mschaf/hp_dl380_fan_controller/reference images/IMG_20200121_184613.jpg

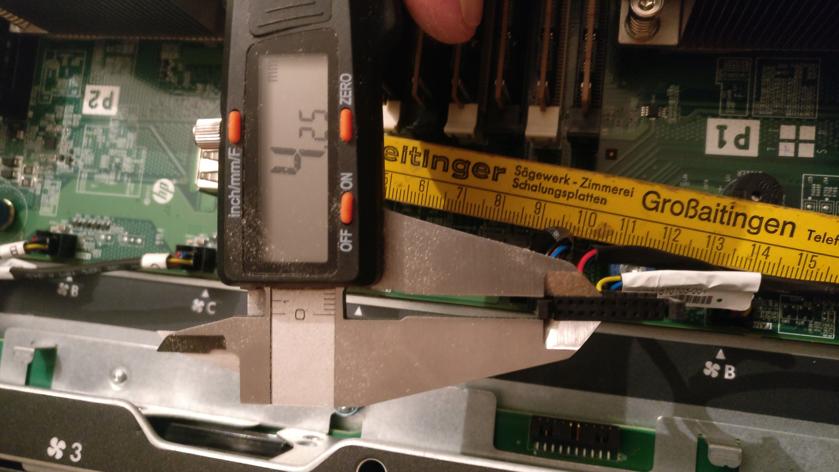
reference images/IMG_20200121_184613.jpg
