mschaf/hp_dl380_fan_controller/reference images/IMG_20200121_184752.jpg

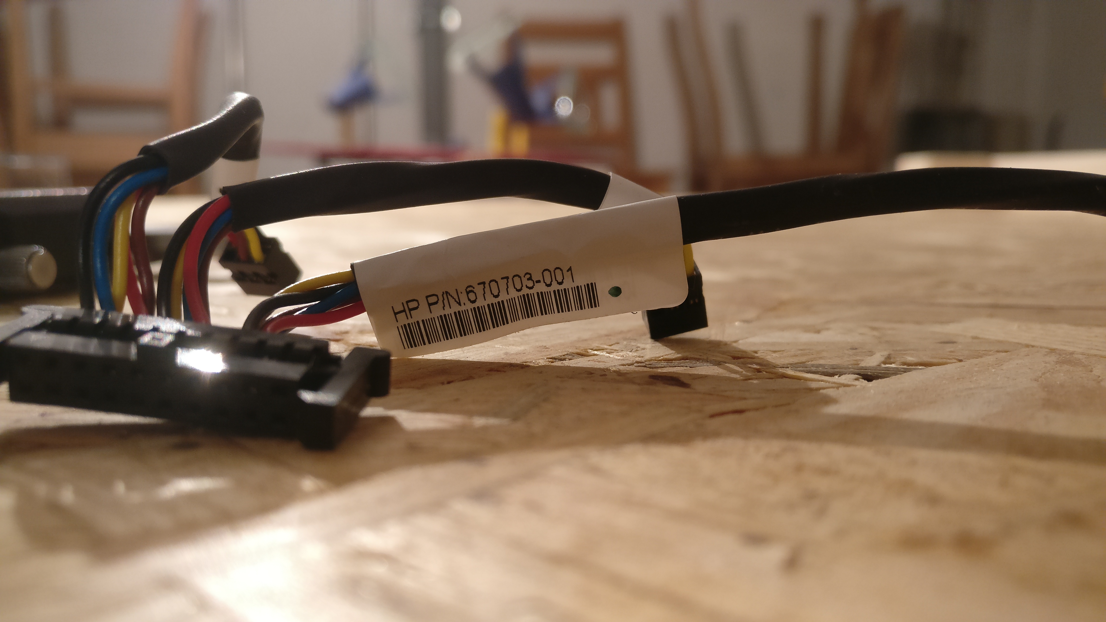
reference images/IMG_20200121_184752.jpg
